Brunomvsilva/KeyTestBox/PCB/KiCadProj/KeyTestBoxLib/Switch/EG1218.step

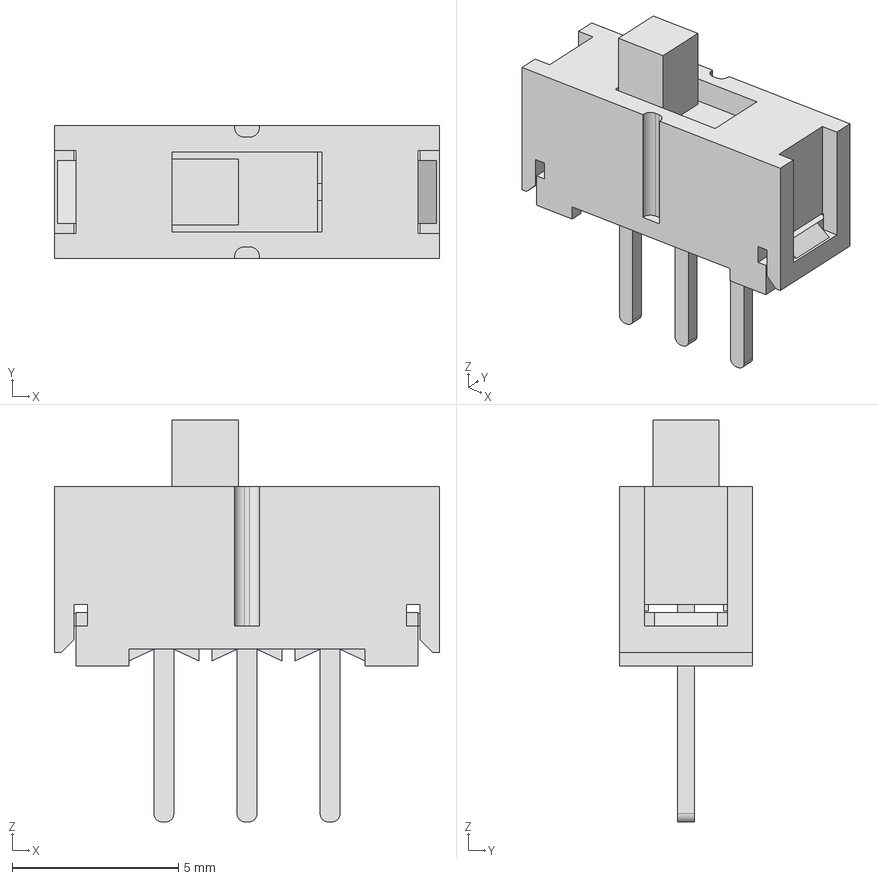
[picture p35: CAD file, 2025-11-05]
PCB/KiCadProj/KeyTestBoxLib/Switch/EG1218.step
11.6 x 4.00 x 12.1 mm
