Brunomvsilva/KeyTestBox/PCB/KiCadProj/KeyTestBoxLib/USBLC6-4SC6/SOT23-6L_STM.step

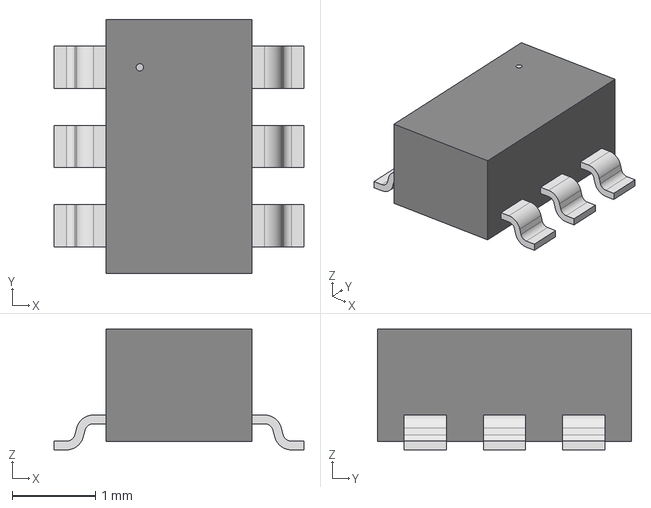
[picture p36: CAD file, 2025-11-05]
PCB/KiCadProj/KeyTestBoxLib/USBLC6-4SC6/SOT23-6L_STM.step
3.00 x 3.05 x 1.45 mm
