Brunomvsilva/KeyTestBox/PCB/KiCadProj/KeyTestBoxLib/2PIN_SCREW_CONN/282837-2.step

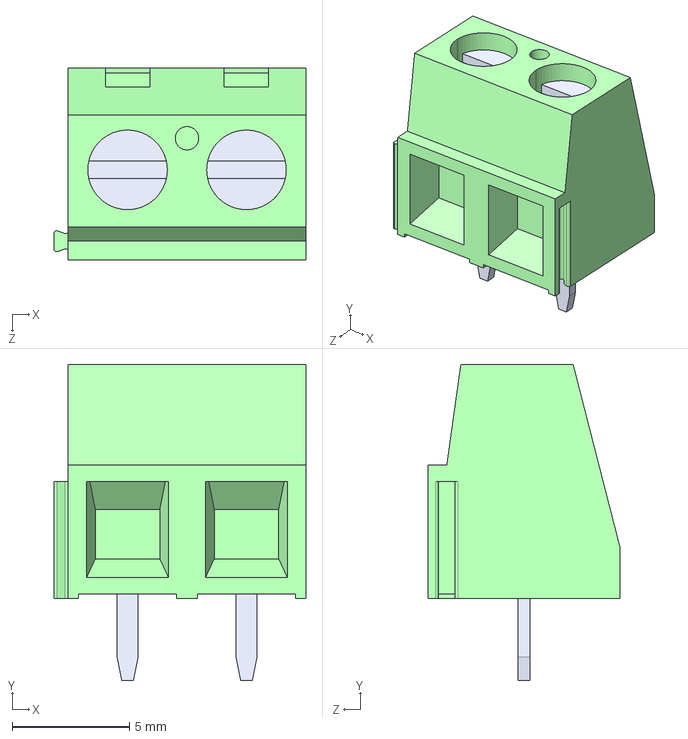
[picture p37: CAD file, 2025-11-05]
PCB/KiCadProj/KeyTestBoxLib/2PIN_SCREW_CONN/282837-2.step
10.8 x 13.5 x 8.20 mm
