Brunomvsilva/KeyTestBox/PCB/KiCadProj/KeyTestBoxLib/7PIN_SCREW_CONN/282837-7/3D/282837-7.stp

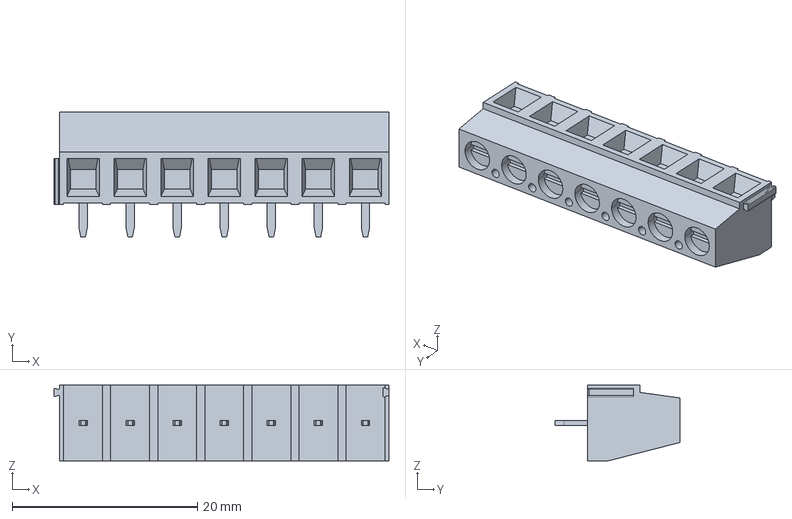
[picture p38: CAD file, 2025-11-05]
PCB/KiCadProj/KeyTestBoxLib/7PIN_SCREW_CONN/282837-7/3D/282837-7.stp
36.2 x 13.5 x 8.20 mm
