Brunomvsilva/KeyTestBox/Tests/LWIP + FREERTOS CUBEMX/LWIP printsv2(or v1)/1.jpg

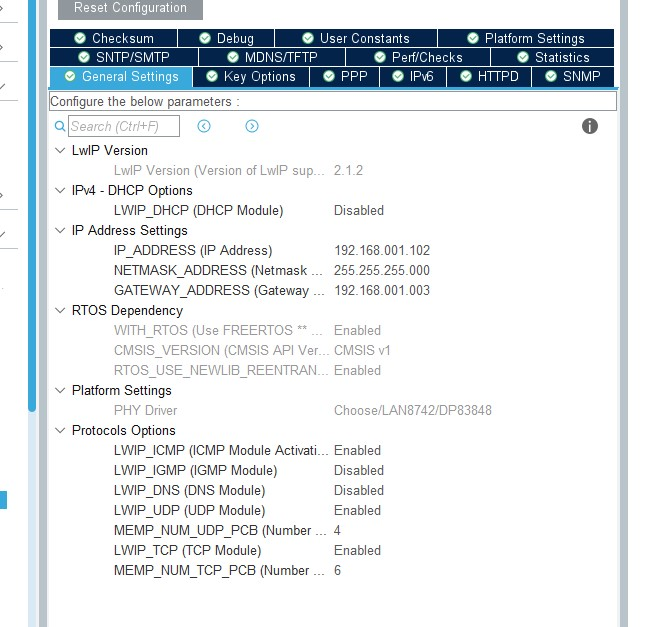
Tests/LWIP + FREERTOS CUBEMX/LWIP printsv2(or v1)/1.jpg
