Brunomvsilva/KeyTestBox/Tests/LWIP + FREERTOS CUBEMX/LWIP printsv2(or v1)/Annotation 2023-11-02 122051.jpg

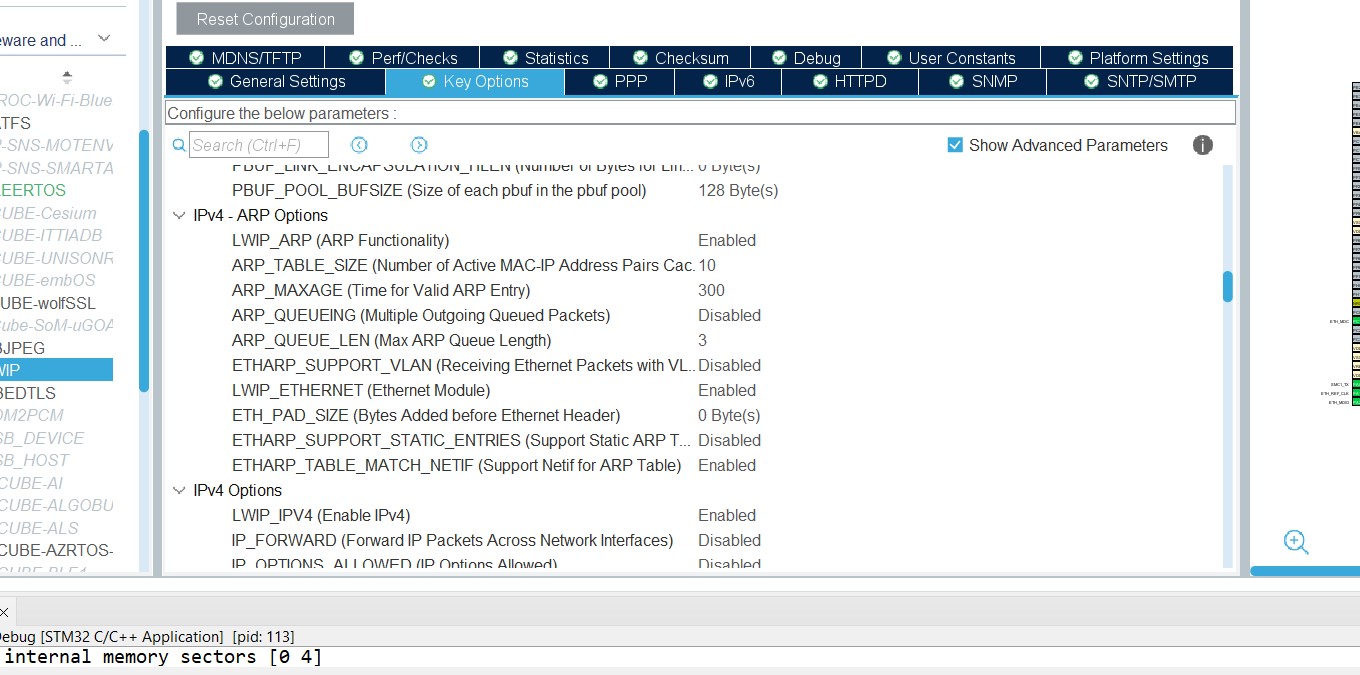
Tests/LWIP + FREERTOS CUBEMX/LWIP printsv2(or v1)/Annotation 2023-11-02 122051.jpg
