Brunomvsilva/KeyTestBox/Tests/ADC_Test/ADC_Test2.jpg

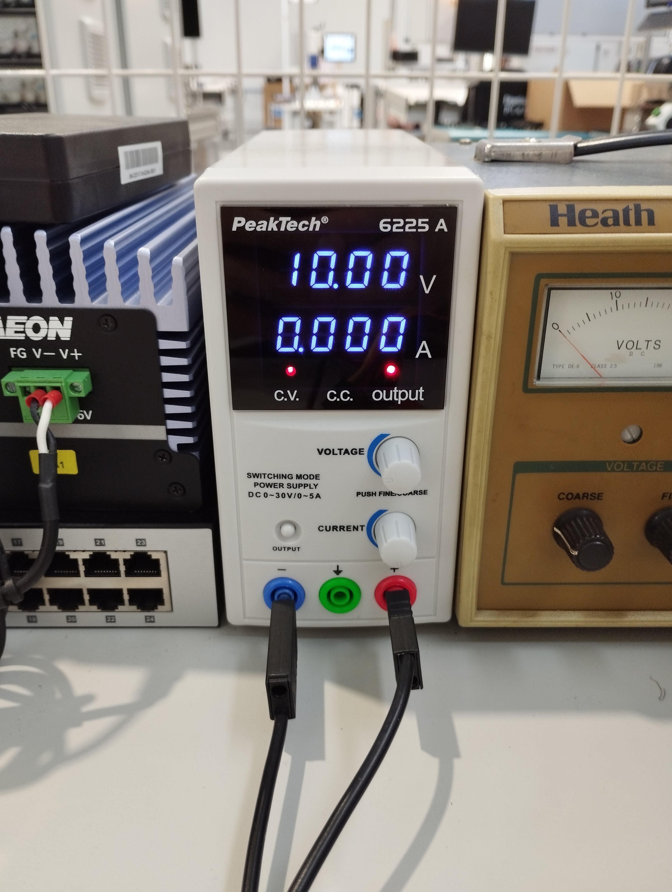
Tests/ADC_Test/ADC_Test2.jpg
