Brunomvsilva/KeyTestBox/Tests/ADC_Test/ADC_Test3.jpg

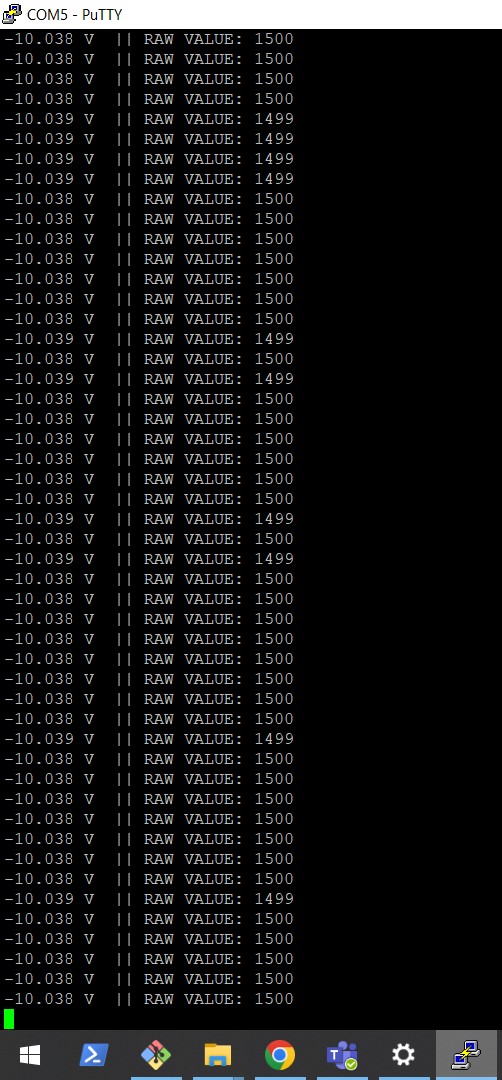
Tests/ADC_Test/ADC_Test3.jpg
