Brunomvsilva/KeyTestBox/Tests/CAN + LIN/CAN TEST 1 KEYTESTBOX.jpg

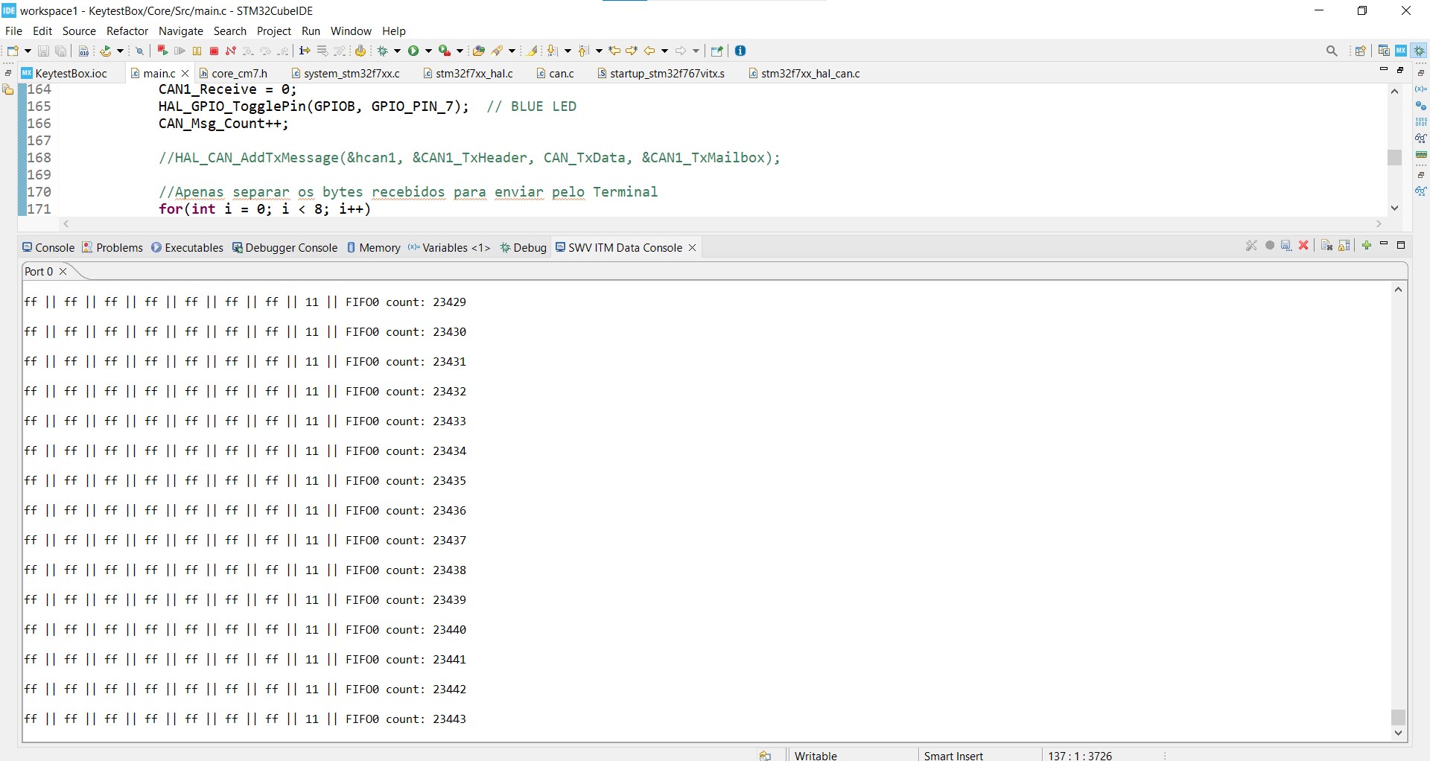
Tests/CAN + LIN/CAN TEST 1 KEYTESTBOX.jpg
