Brunomvsilva/KeyTestBox/Tests/CAN + LIN/CAN TEST 2 KEYTESTBOX.jpg

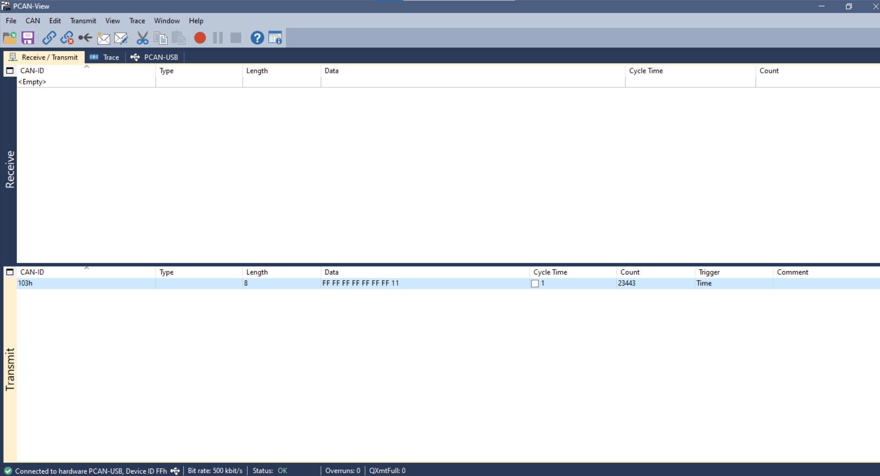
Tests/CAN + LIN/CAN TEST 2 KEYTESTBOX.jpg
