Brunomvsilva/KeyTestBox/Tests/CAN + LIN/LIN Data ID 3Ah.jpg

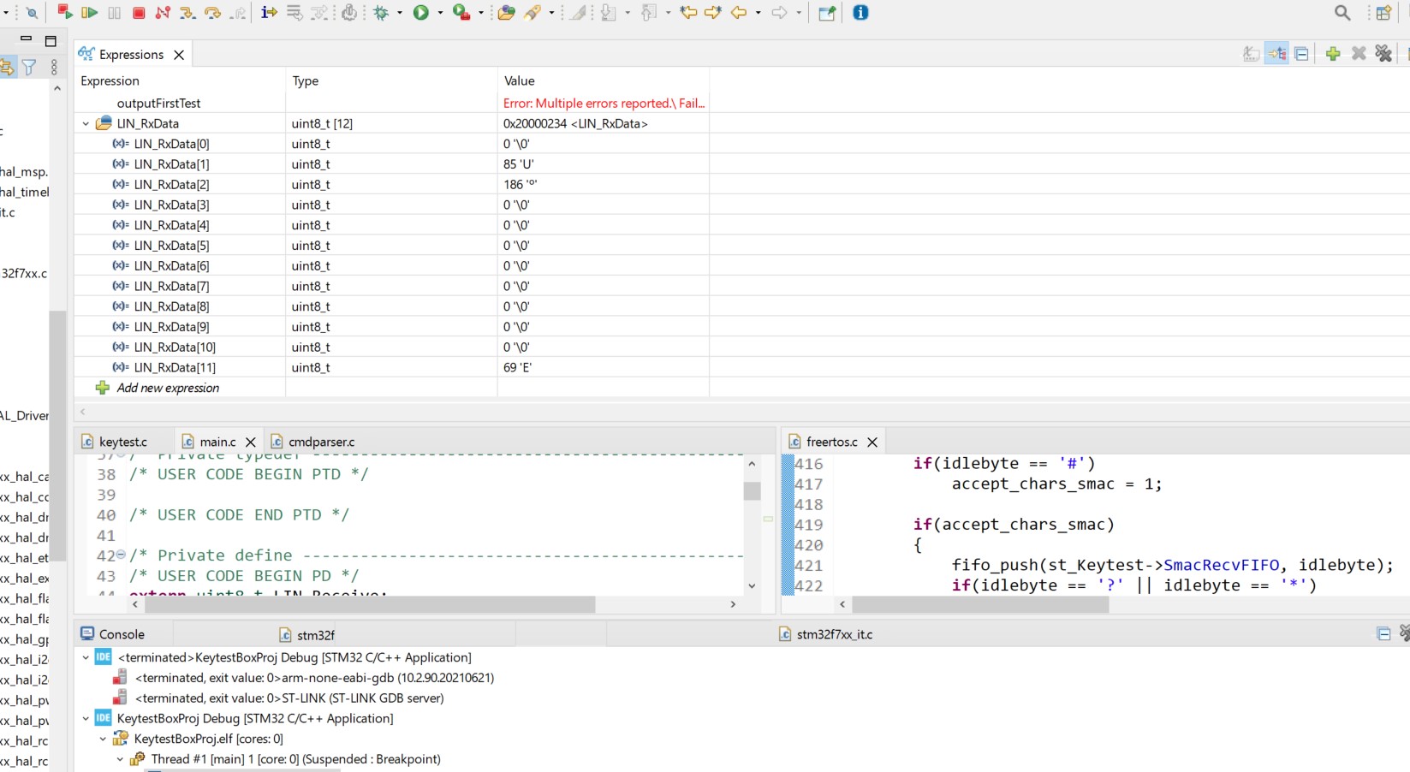
Tests/CAN + LIN/LIN Data ID 3Ah.jpg
