Brunomvsilva/KeyTestBox/Tests/CAN + LIN/MicrosoftTeams-image.png

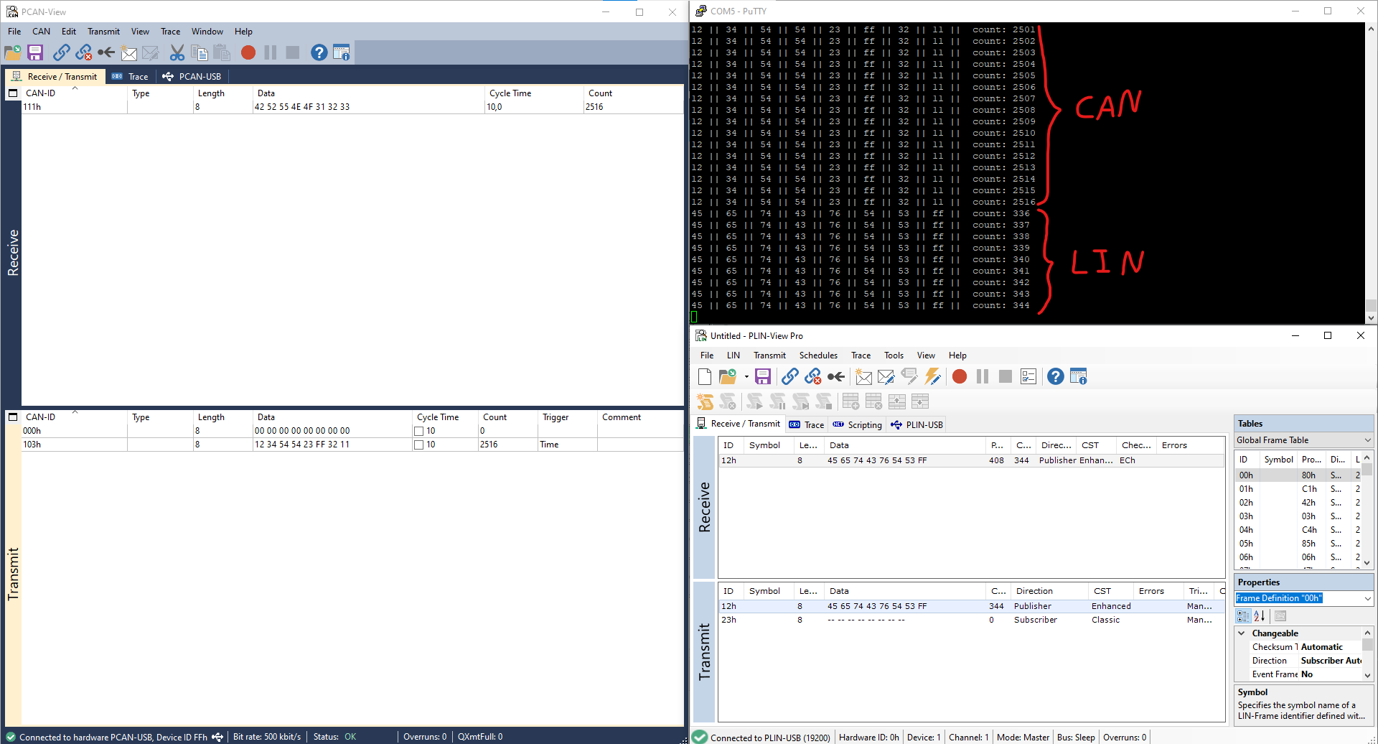
Tests/CAN + LIN/MicrosoftTeams-image.png
