Brunomvsilva/KeyTestBox/Tests/Final Tests/Só Alavanca/1250_alavanca3.jpg

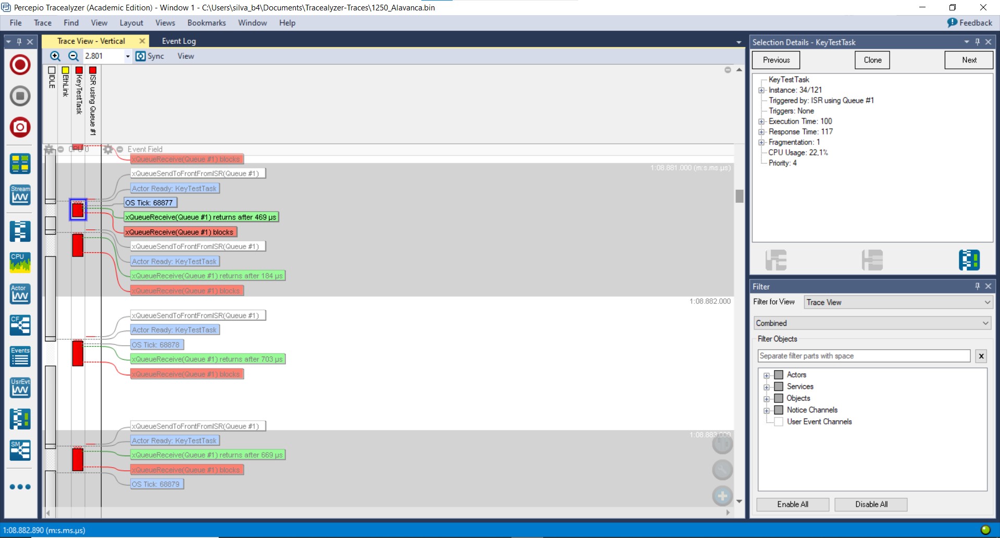
Tests/Final Tests/Só Alavanca/1250_alavanca3.jpg
