Brunomvsilva/KeyTestBox/Tests/Final Tests/Só Alavanca/1250_alavanca4.jpg

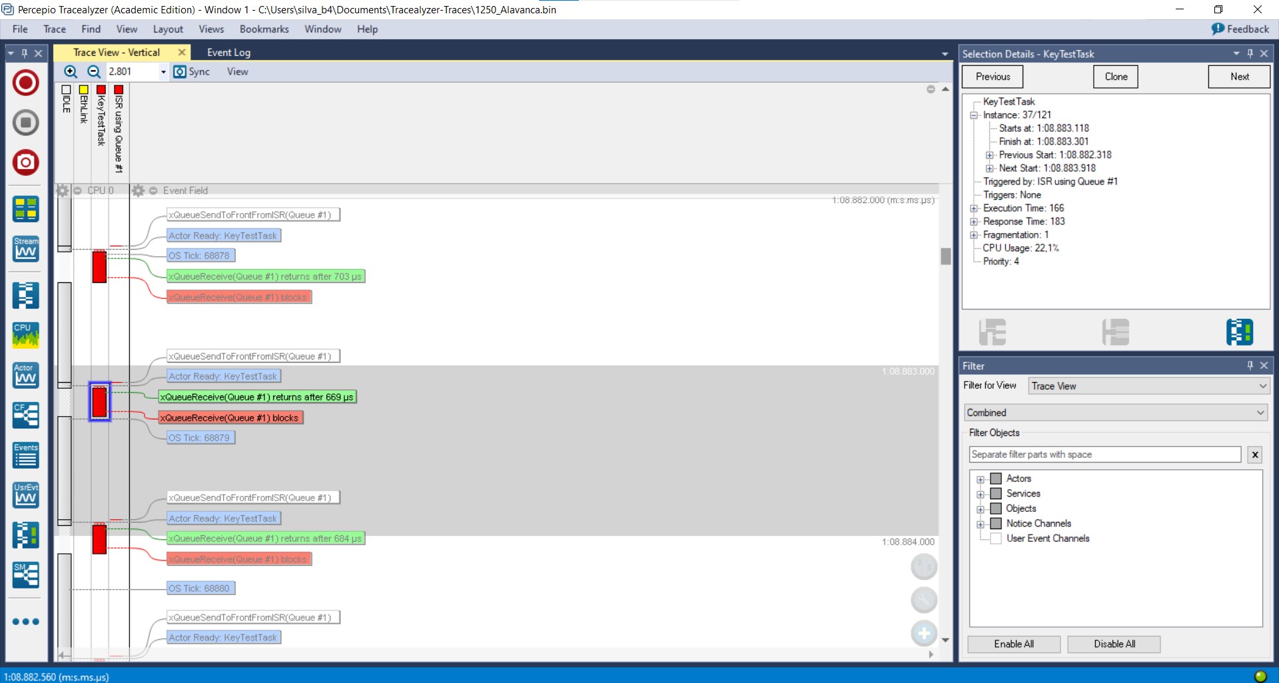
Tests/Final Tests/Só Alavanca/1250_alavanca4.jpg
