Brunomvsilva/KeyTestBox/Tests/Final Tests/Só Alavanca/TCPIP_Thread2.jpg

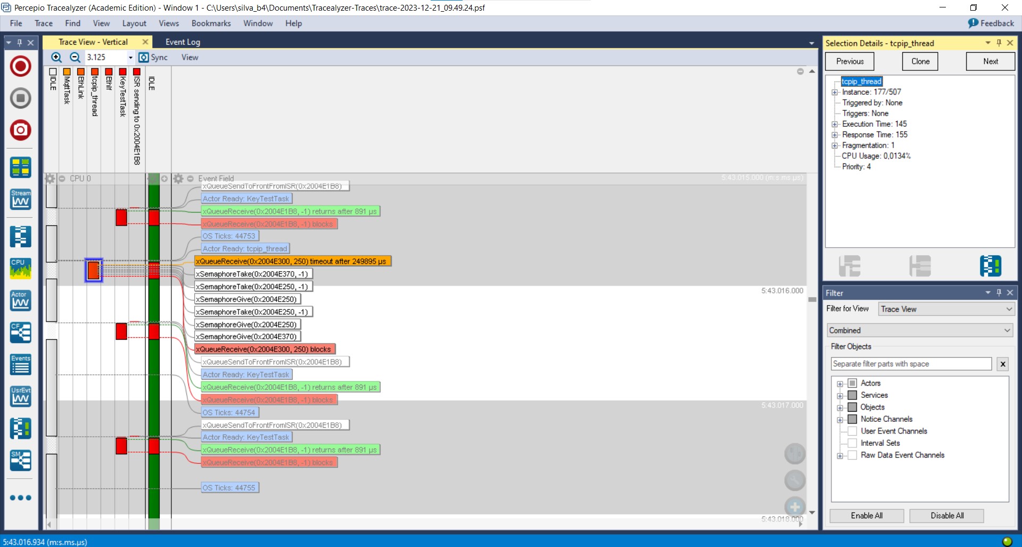
Tests/Final Tests/Só Alavanca/TCPIP_Thread2.jpg
