Brunomvsilva/KeyTestBox/Tests/Final Tests/Só Alavanca/TCPIP_Thread.jpg

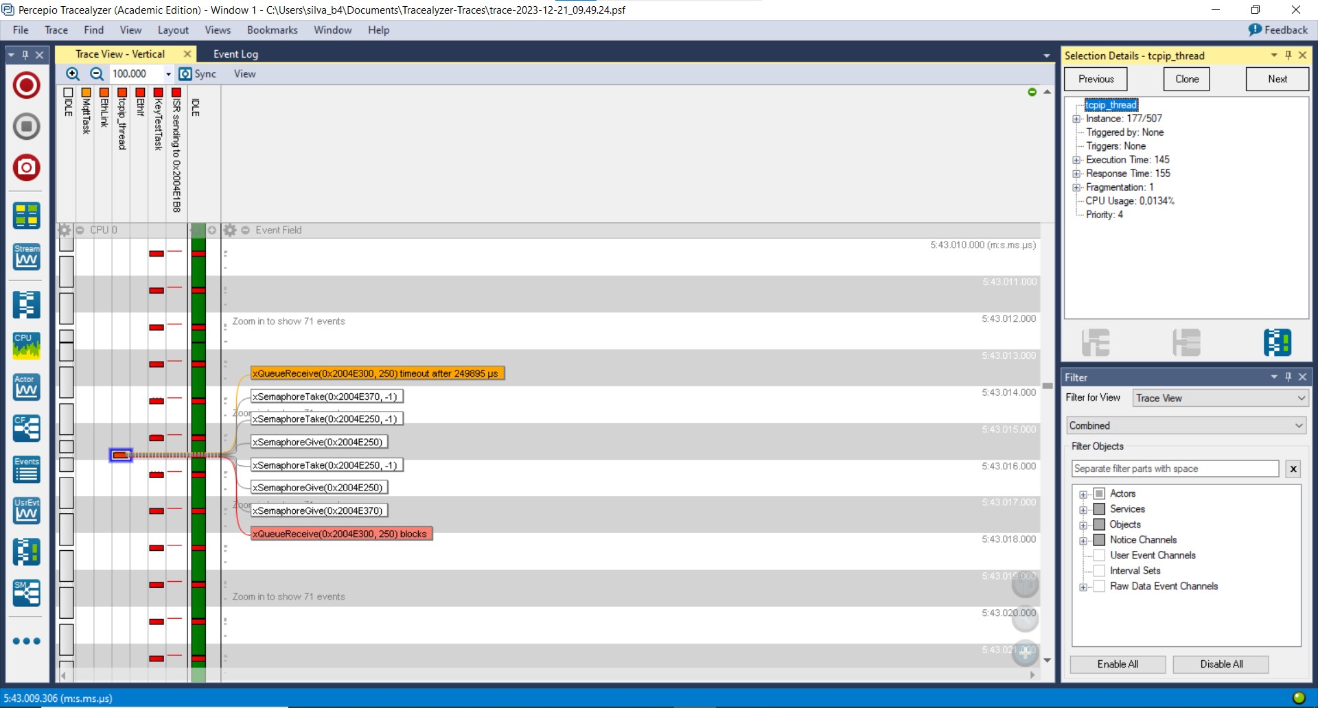
Tests/Final Tests/Só Alavanca/TCPIP_Thread.jpg
