Brunomvsilva/KeyTestBox/Tests/LWIP + FREERTOS CUBEMX/ETH1.jpg

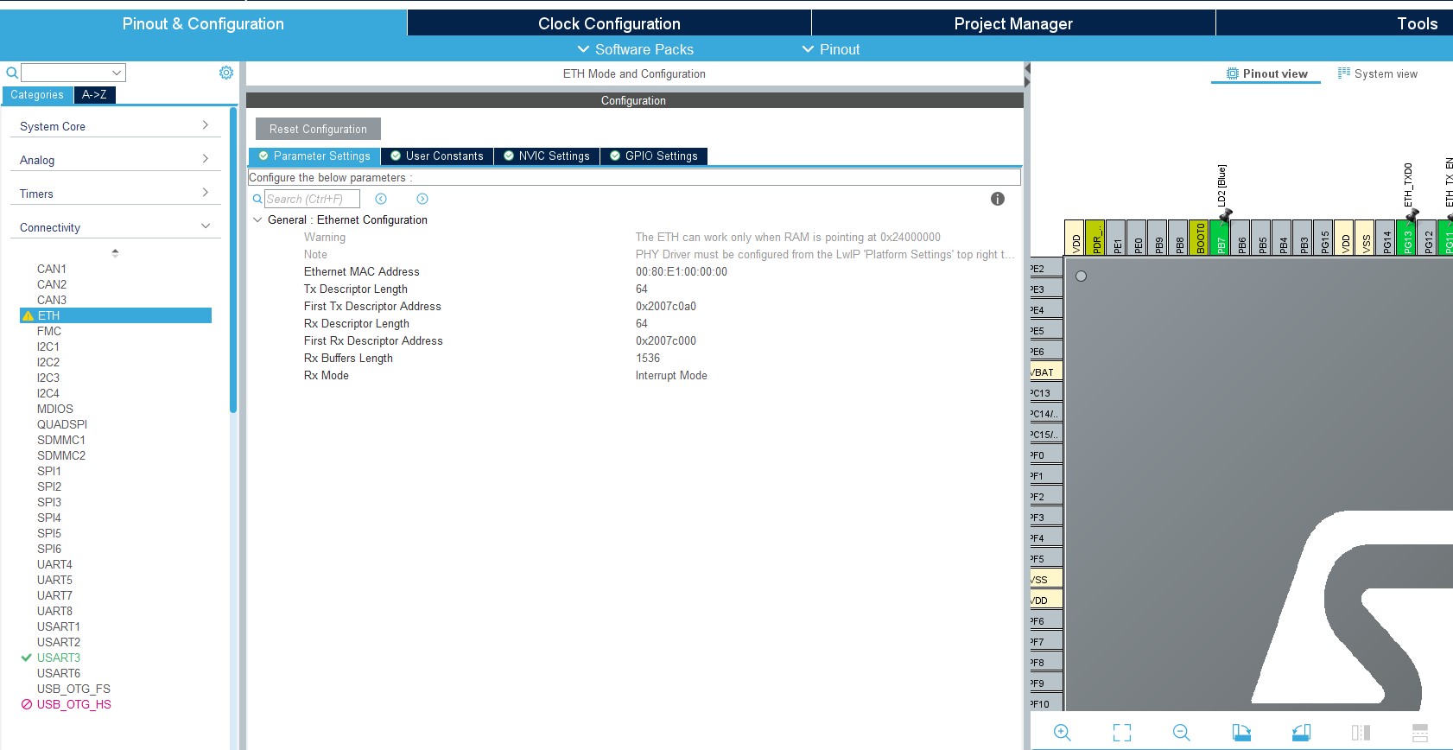
Tests/LWIP + FREERTOS CUBEMX/ETH1.jpg
