Brunomvsilva/KeyTestBox/Tests/LWIP + FREERTOS CUBEMX/freertos1.jpg

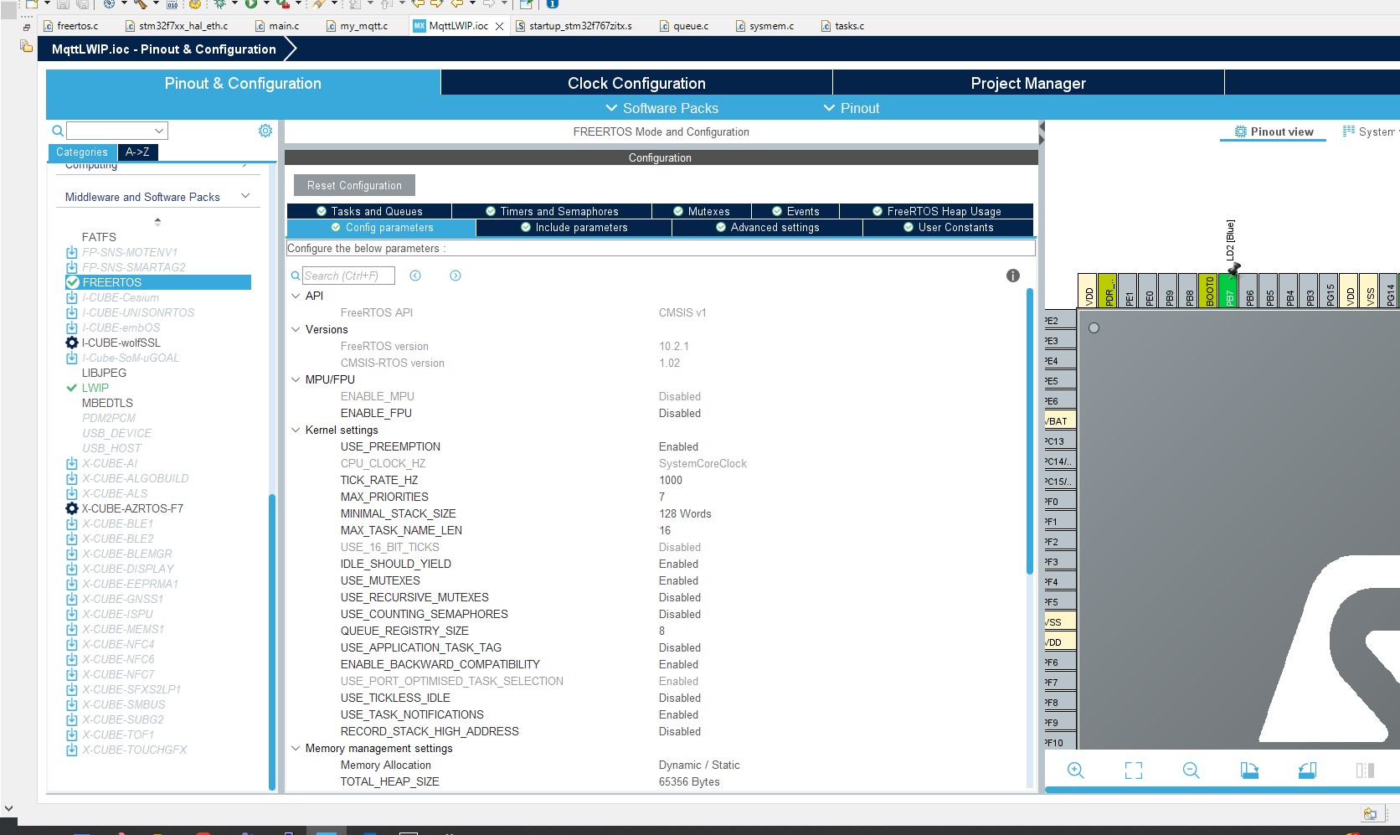
Tests/LWIP + FREERTOS CUBEMX/freertos1.jpg
