Brunomvsilva/KeyTestBox/Tests/LWIP + FREERTOS CUBEMX/freertos2.jpg

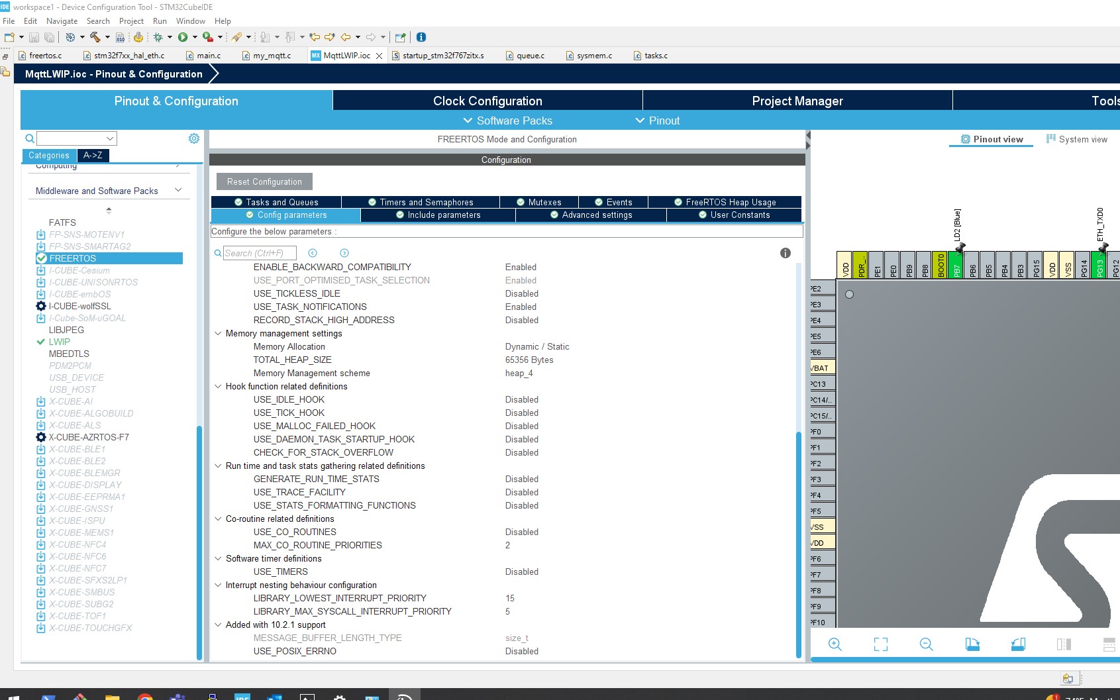
Tests/LWIP + FREERTOS CUBEMX/freertos2.jpg
