Brunomvsilva/KeyTestBox/Tests/LWIP + FREERTOS CUBEMX/freertos3.jpg

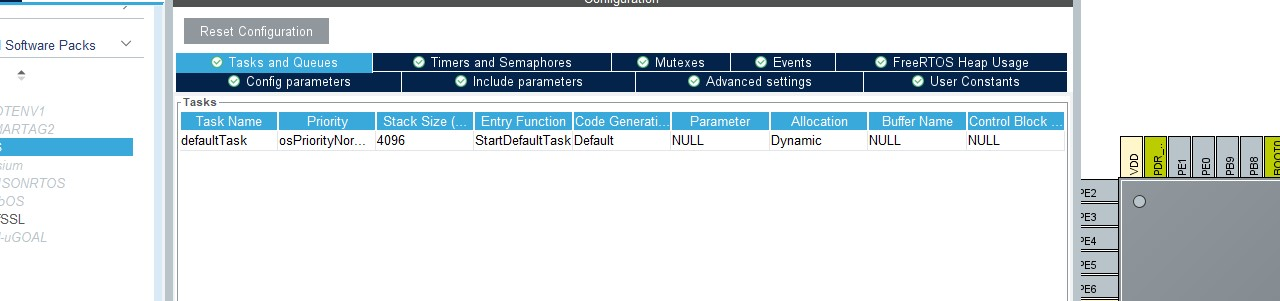
Tests/LWIP + FREERTOS CUBEMX/freertos3.jpg
