Brunomvsilva/KeyTestBox/Tests/LWIP + FREERTOS CUBEMX/LWIP1.jpg

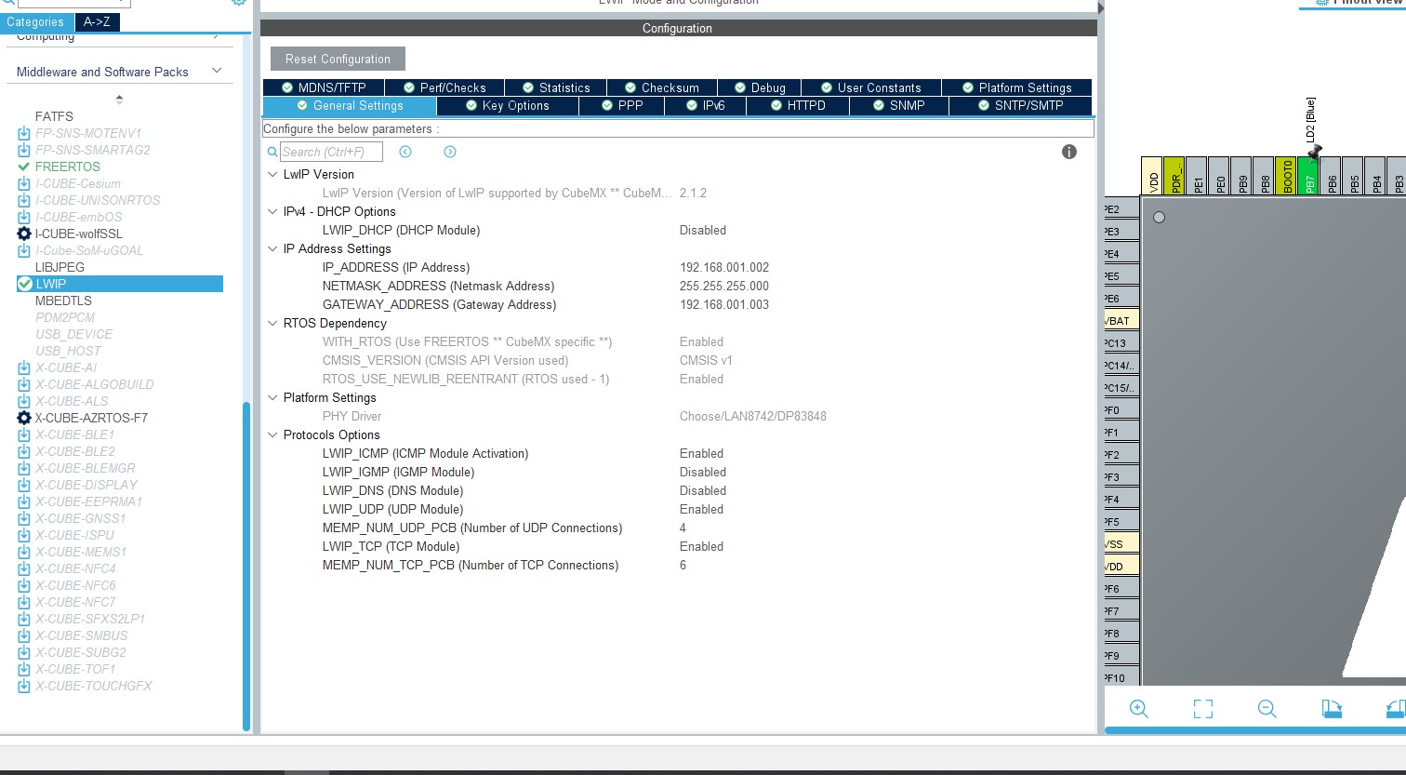
Tests/LWIP + FREERTOS CUBEMX/LWIP1.jpg
