Brunomvsilva/KeyTestBox/Tests/LWIP + FREERTOS CUBEMX/LWIP2.jpg

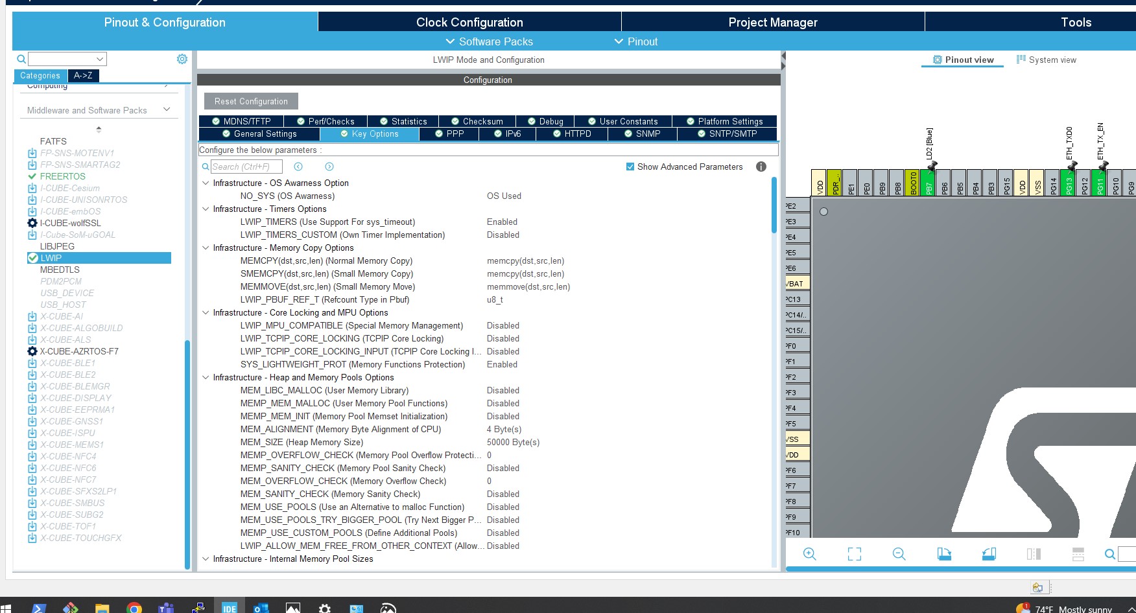
Tests/LWIP + FREERTOS CUBEMX/LWIP2.jpg
