Brunomvsilva/KeyTestBox/Tests/LWIP + FREERTOS CUBEMX/LWIP3.jpg

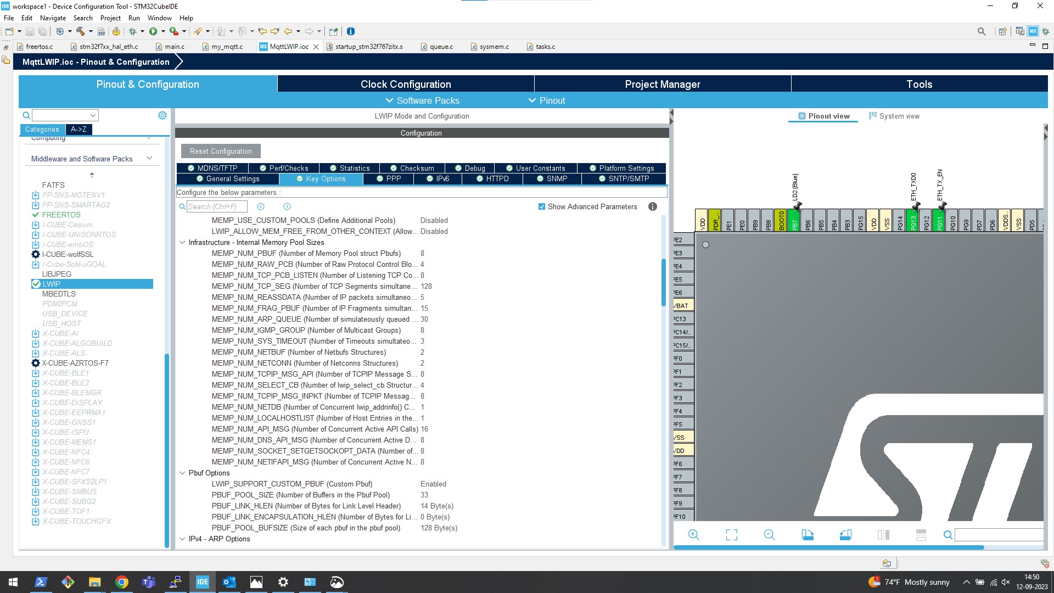
Tests/LWIP + FREERTOS CUBEMX/LWIP3.jpg
