Brunomvsilva/KeyTestBox/Tests/LWIP + FREERTOS CUBEMX/LWIP5.jpg

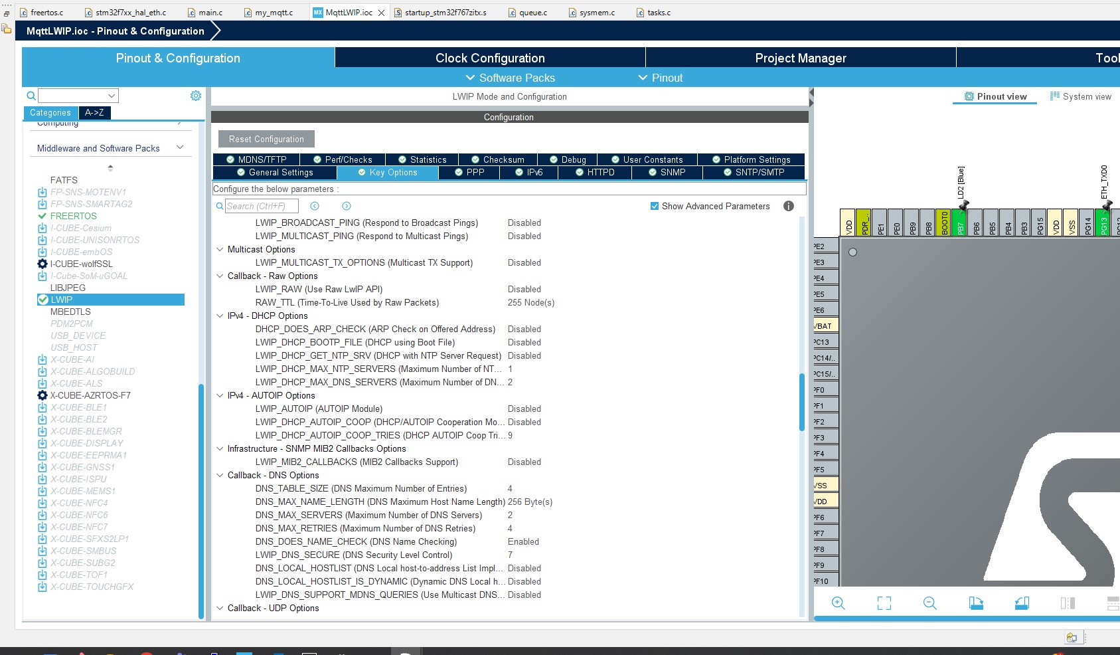
Tests/LWIP + FREERTOS CUBEMX/LWIP5.jpg
