Brunomvsilva/KeyTestBox/Tests/LWIP + FREERTOS CUBEMX/LWIP6.jpg

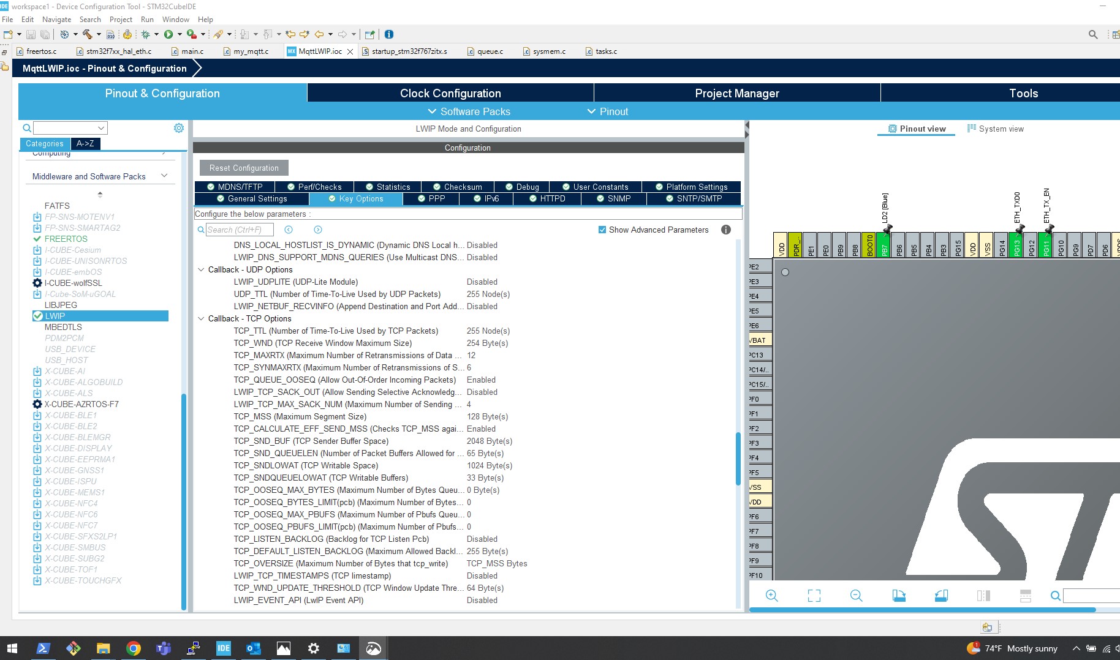
Tests/LWIP + FREERTOS CUBEMX/LWIP6.jpg
