Brunomvsilva/KeyTestBox/Tests/LWIP + FREERTOS CUBEMX/LWIP7.jpg

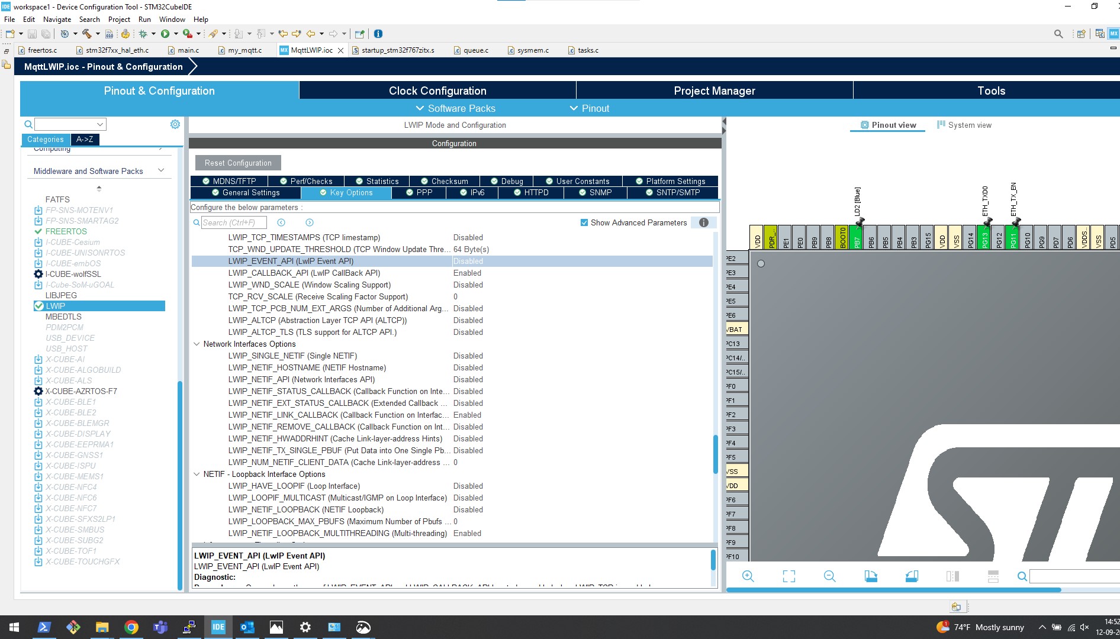
Tests/LWIP + FREERTOS CUBEMX/LWIP7.jpg
