Brunomvsilva/KeyTestBox/Tests/LWIP + FREERTOS CUBEMX/LWIP9.jpg

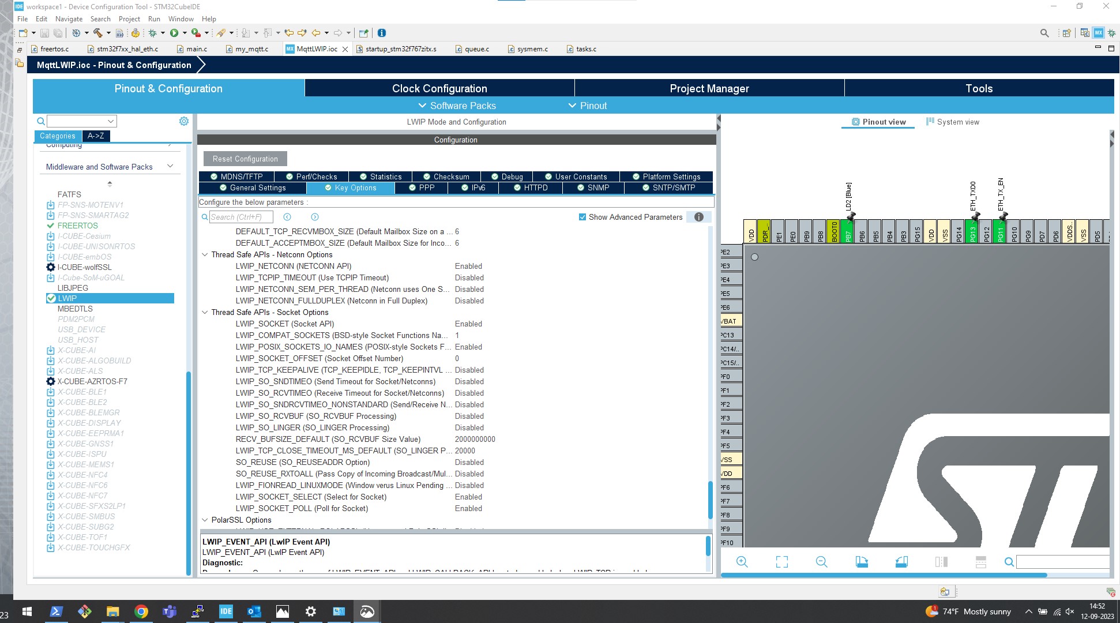
Tests/LWIP + FREERTOS CUBEMX/LWIP9.jpg
