Brunomvsilva/KeyTestBox/Tests/LWIP + FREERTOS CUBEMX/LWIP10.jpg

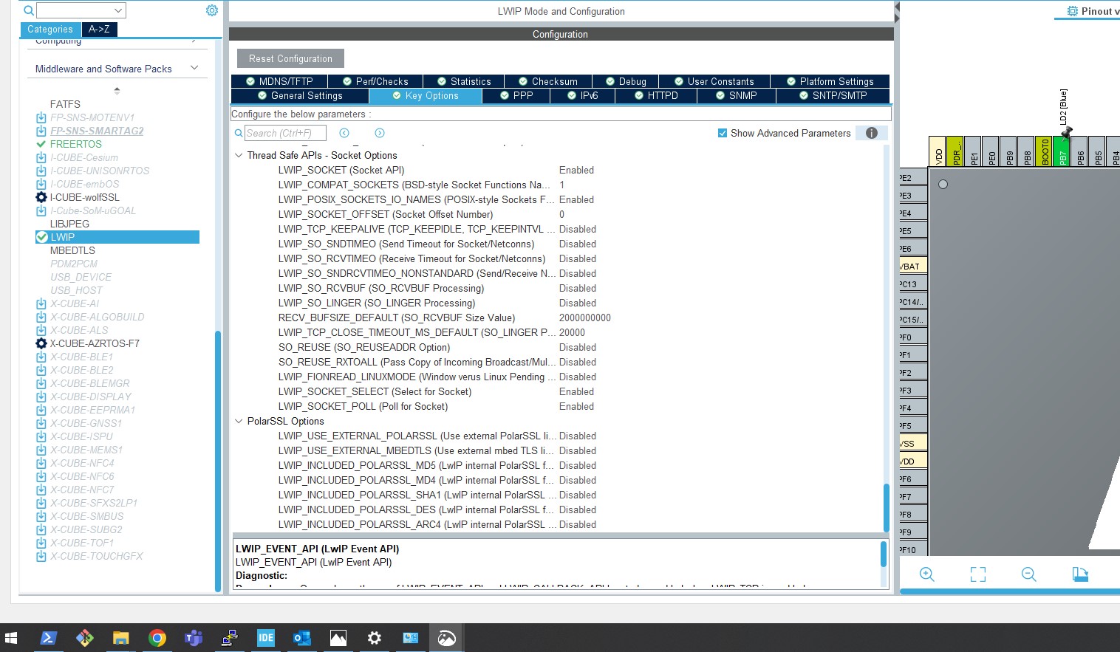
Tests/LWIP + FREERTOS CUBEMX/LWIP10.jpg
