Brunomvsilva/KeyTestBox/KeytestBoxProj/Core/Src/can.c

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
/* Includes ------------------------------------------------------------------*/
#include "can.h"

CAN_HandleTypeDef hcan1;

/* CAN1 init function */
void MX_CAN1_Init(void)
{

  hcan1.Instance = CAN1;
  hcan1.Init.Prescaler = 6;
  hcan1.Init.Mode = CAN_MODE_NORMAL;
  hcan1.Init.SyncJumpWidth = CAN_SJW_1TQ;
  hcan1.Init.TimeSeg1 = CAN_BS1_16TQ;
  hcan1.Init.TimeSeg2 = CAN_BS2_1TQ;
  hcan1.Init.TimeTriggeredMode = DISABLE;
  hcan1.Init.AutoBusOff = DISABLE;
  hcan1.Init.AutoWakeUp = DISABLE;
  hcan1.Init.AutoRetransmission = DISABLE;
  hcan1.Init.ReceiveFifoLocked = DISABLE;
  hcan1.Init.TransmitFifoPriority = DISABLE;
  if (HAL_CAN_Init(&hcan1) != HAL_OK)
  {
    Error_Handler();
  }
  /* USER CODE BEGIN CAN1_Init 2 */
//  CAN_FilterTypeDef canfilterconfig0, canfilterconfig1;
//
//  // Configure the first filter for RxFIFO0
//  canfilterconfig0.FilterActivation = CAN_FILTER_ENABLE;
//  canfilterconfig0.FilterBank = 0;  // Choose a suitable filter bank
//  canfilterconfig0.FilterFIFOAssignment = CAN_RX_FIFO0;
//  canfilterconfig0.FilterIdHigh = 0x103 << 5;  // Set the ID you want to allow (0x102)
//  canfilterconfig0.FilterIdLow = 0x0000;
//  canfilterconfig0.FilterMaskIdHigh = 0x7FF << 5;  // Set mask to accept all bits in ID
//  canfilterconfig0.FilterMaskIdLow = 0x0000;
//  canfilterconfig0.FilterMode = CAN_FILTERMODE_IDMASK;
//  canfilterconfig0.FilterScale = CAN_FILTERSCALE_32BIT;
//  canfilterconfig0.SlaveStartFilterBank = 0;  // Not used for the first filter
//  HAL_CAN_ConfigFilter(&hcan1, &canfilterconfig0);
  /* USER CODE END CAN1_Init 2 */

}

void HAL_CAN_MspInit(CAN_HandleTypeDef* canHandle)
{

  GPIO_InitTypeDef GPIO_InitStruct = {0};
  if(canHandle->Instance==CAN1)
  {
    /* CAN1 clock enable */
    __HAL_RCC_CAN1_CLK_ENABLE();

    __HAL_RCC_GPIOB_CLK_ENABLE();
    /**CAN1 GPIO Configuration
    PB8     ------> CAN1_RX
    PB9     ------> CAN1_TX
    */
    GPIO_InitStruct.Pin = GPIO_PIN_8|GPIO_PIN_9;
    GPIO_InitStruct.Mode = GPIO_MODE_AF_PP;
    GPIO_InitStruct.Pull = GPIO_NOPULL;
    GPIO_InitStruct.Speed = GPIO_SPEED_FREQ_VERY_HIGH;
    GPIO_InitStruct.Alternate = GPIO_AF9_CAN1;
    HAL_GPIO_Init(GPIOB, &GPIO_InitStruct);

    /* CAN1 interrupt Init */
    HAL_NVIC_SetPriority(CAN1_RX0_IRQn, 5, 0);
    HAL_NVIC_EnableIRQ(CAN1_RX0_IRQn);
    HAL_NVIC_SetPriority(CAN1_RX1_IRQn, 5, 0);
    HAL_NVIC_EnableIRQ(CAN1_RX1_IRQn);
  }
}

void HAL_CAN_MspDeInit(CAN_HandleTypeDef* canHandle)
{

  if(canHandle->Instance==CAN1)
  {
    /* Peripheral clock disable */
    __HAL_RCC_CAN1_CLK_DISABLE();

    /**CAN1 GPIO Configuration
    PB8     ------> CAN1_RX
    PB9     ------> CAN1_TX
    */
    HAL_GPIO_DeInit(GPIOB, GPIO_PIN_8|GPIO_PIN_9);

    /* CAN1 interrupt Deinit */
    HAL_NVIC_DisableIRQ(CAN1_RX0_IRQn);
    HAL_NVIC_DisableIRQ(CAN1_RX1_IRQn);
  }
}
